onuremirhancon/Wind-Turbine-Battery-Charger/Simulation/Spice_1/Buck_Lowside.asc

C2: cap; 10µ
D1: diode
L1: ind; 100µ
M1: nmos; IRFZ44N
R1: res; 75m
R2: res; 4.7
V1: voltage; 20
V2: voltage; PULSE(-4 10 1u 10n 50n 5u 10u)
Named nets: GateTop, SourceTop, in, out, 0
.tran 0 10m 0
