onuremirhancon/Wind-Turbine-Battery-Charger/Simulation/Spice_1/FBDR.asc

C1: cap; 1mF
D1: schottky; RBR10T60ANZ
D2: schottky; RBR10T60ANZ
D3: schottky; RBR10T60ANZ
D4: schottky; RBR10T60ANZ
D5: schottky; RBR10T60ANZ
D6: schottky; RBR10T60ANZ
I1: current; 10
R1: res; 47K
R2: res; 0.1
V1: voltage; SINE(0 {Vp} 50 0 0 0 100)
V2: voltage; SINE(0 {Vp} 50 -6.667e-3 0 0 100)
V3: voltage; SINE(0 {Vp} 50 -0.13333 0 0 100)
Named nets: 0, Phase_A, Phase_B, Phase_C, Vout
.step param Vp 12.4 20.4 1
.tran 0 100m 60m
.meas Diode_Pavg  AVG V(Phase_A, Vout)*I(D1)
.meas Vout_avg AVG V(vout)
.meas TRAN Vmax MAX V(vout)
.meas TRAN Vmin MIN V(vout)
.meas TRAN Imax MAX I(D1)
.meas TRAN Imin MIN I(D1)
